EE-crisrmh/Arduino-EEPROM-PROGRAMMER/Doc/Arduino EEPROGAMMER schematic.kicad_sch

## KiCad design Doc/Arduino EEPROGAMMER schematic.kicad_sch (2026-02-18)

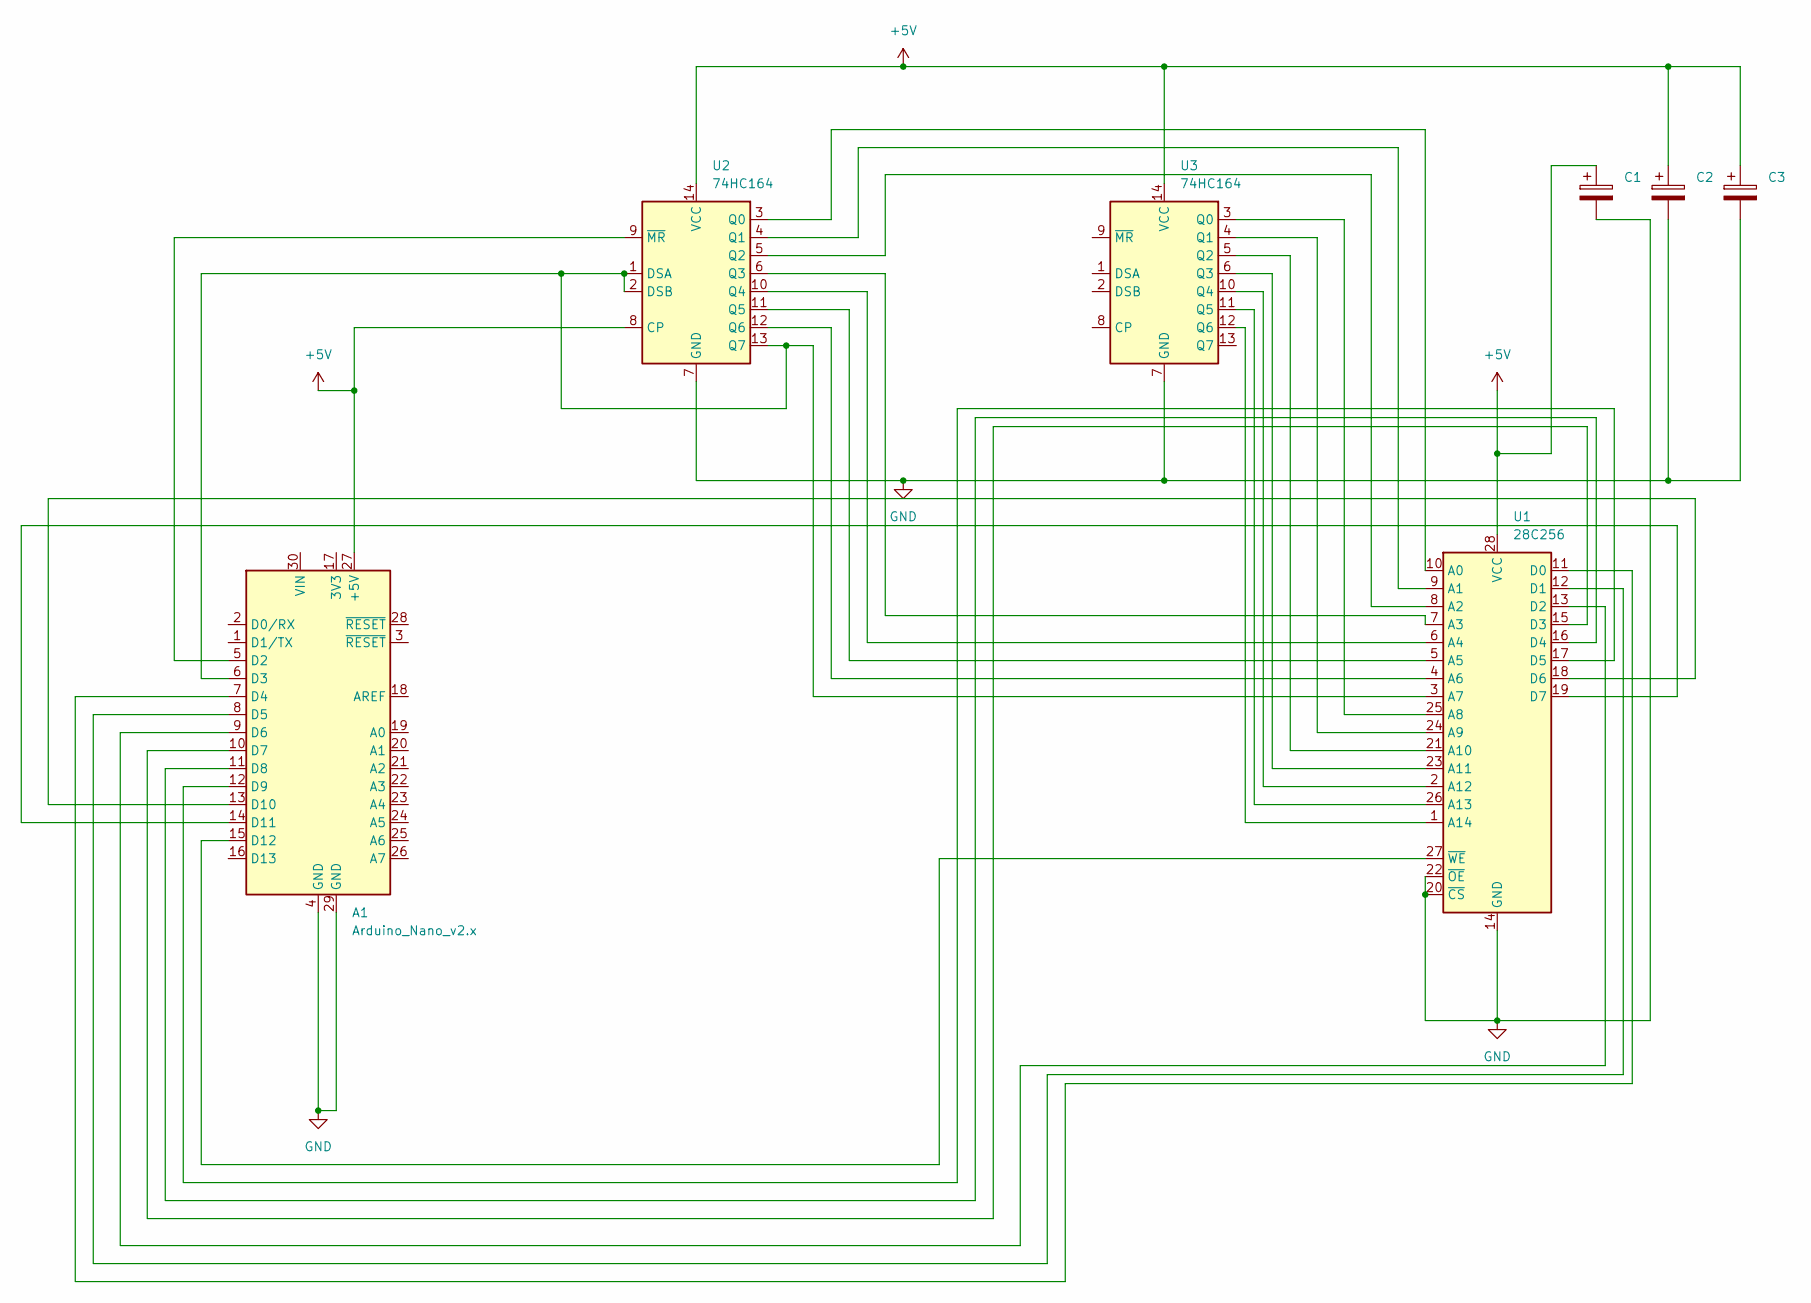
[picture p3: schematic Arduino EEPROGAMMER schematic.kicad_sch]

Parts:
A1: Arduino_Nano_v2.x; Arduino_Nano
C1, C2, C3: C_Polarized
U1: 28C256
U2, U3: 74HC164

Connections:
+5V: A1.27 (+5V), C1.1, C2.1, C3.1, U1.28 (VCC), U2.8 (CP), U2.14 (VCC), U3.14 (VCC)
GND: A1.4 (GND), A1.29 (GND), C1.2, C2.2, C3.2, U1.14 (GND), U1.20 (~CS), U1.22 (~OE), U2.7 (GND), U3.7 (GND)
unnamed: A1.5 (D2), U2.9 (~MR)
unnamed: A1.6 (D3), U1.3 (A7), U2.1 (DSA), U2.2 (DSB), U2.13 (Q7)
unnamed: A1.7 (D4), U1.11 (D0)
unnamed: A1.8 (D5), U1.12 (D1)
unnamed: A1.9 (D6), U1.13 (D2)
unnamed: A1.10 (D7), U1.15 (D3)
unnamed: A1.11 (D8), U1.16 (D4)
unnamed: A1.12 (D9), U1.17 (D5)
unnamed: A1.13 (D10), U1.18 (D6)
unnamed: A1.14 (D11), U1.19 (D7)
unnamed: A1.15 (D12), U1.27 (~WE)
unnamed: U1.1 (A14), U3.12 (Q6)
unnamed: U1.2 (A12), U3.10 (Q4)
unnamed: U1.4 (A6), U2.12 (Q6)
unnamed: U1.5 (A5), U2.11 (Q5)
unnamed: U1.6 (A4), U2.10 (Q4)
unnamed: U1.7 (A3), U2.6 (Q3)
unnamed: U1.8 (A2), U2.5 (Q2)
unnamed: U1.9 (A1), U2.4 (Q1)
unnamed: U1.10 (A0), U2.3 (Q0)
unnamed: U1.21 (A10), U3.5 (Q2)
unnamed: U1.23 (A11), U3.6 (Q3)
unnamed: U1.24 (A9), U3.4 (Q1)
unnamed: U1.25 (A8), U3.3 (Q0)
unnamed: U1.26 (A13), U3.11 (Q5)
